mrk-fox/MHIPS/pictures/big_example_tile.png

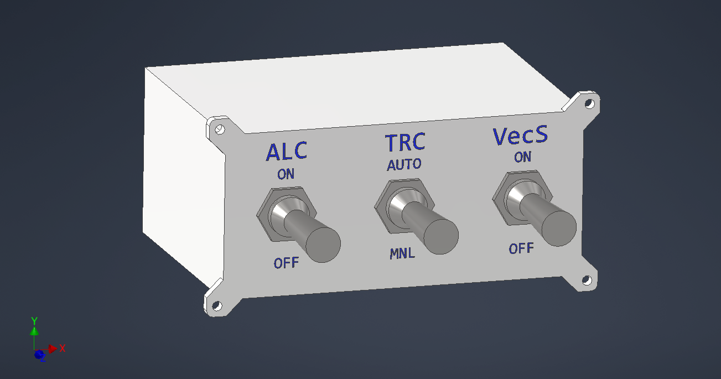
pictures/big_example_tile.png
